awesomebrownies/cyberdeck/CAD/Trigger.step

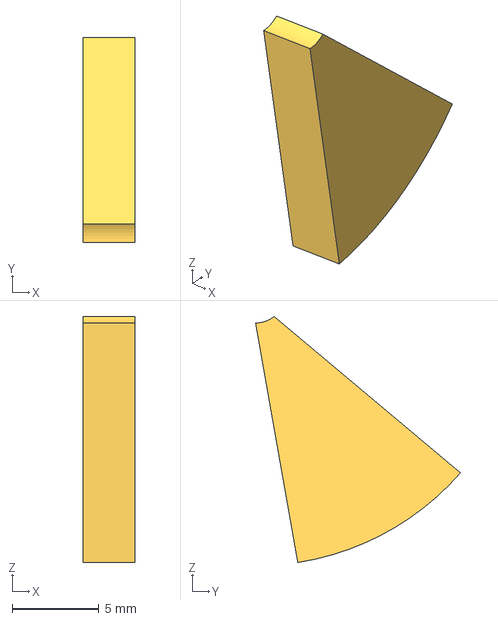
[picture p15: CAD file, 2025-06-18]
CAD/Trigger.step
3.00 x 11.8 x 14.2 mm
